ShenYiTan/self-balancing-robot-esp32/docs/images/IMG_20250817_193725.jpg

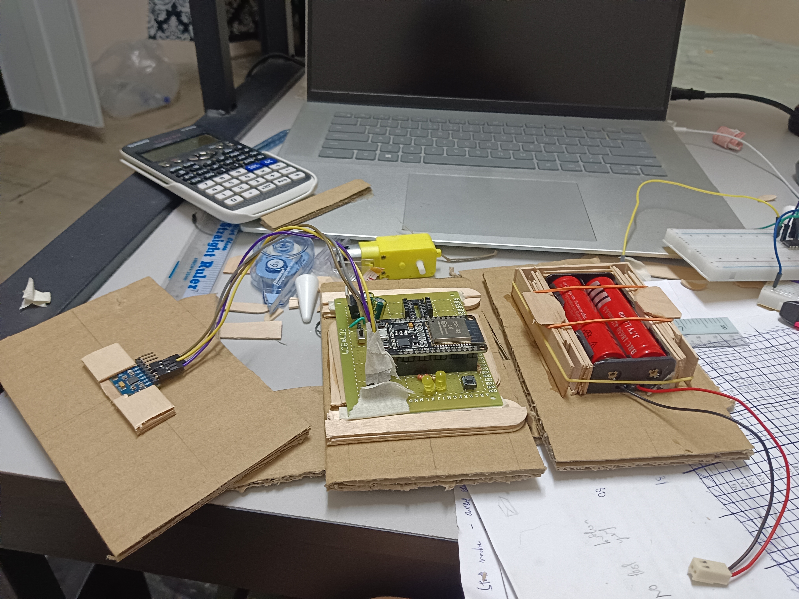
docs/images/IMG_20250817_193725.jpg
