ShenYiTan/self-balancing-robot-esp32/docs/images/IMG_20250912_112348.jpg

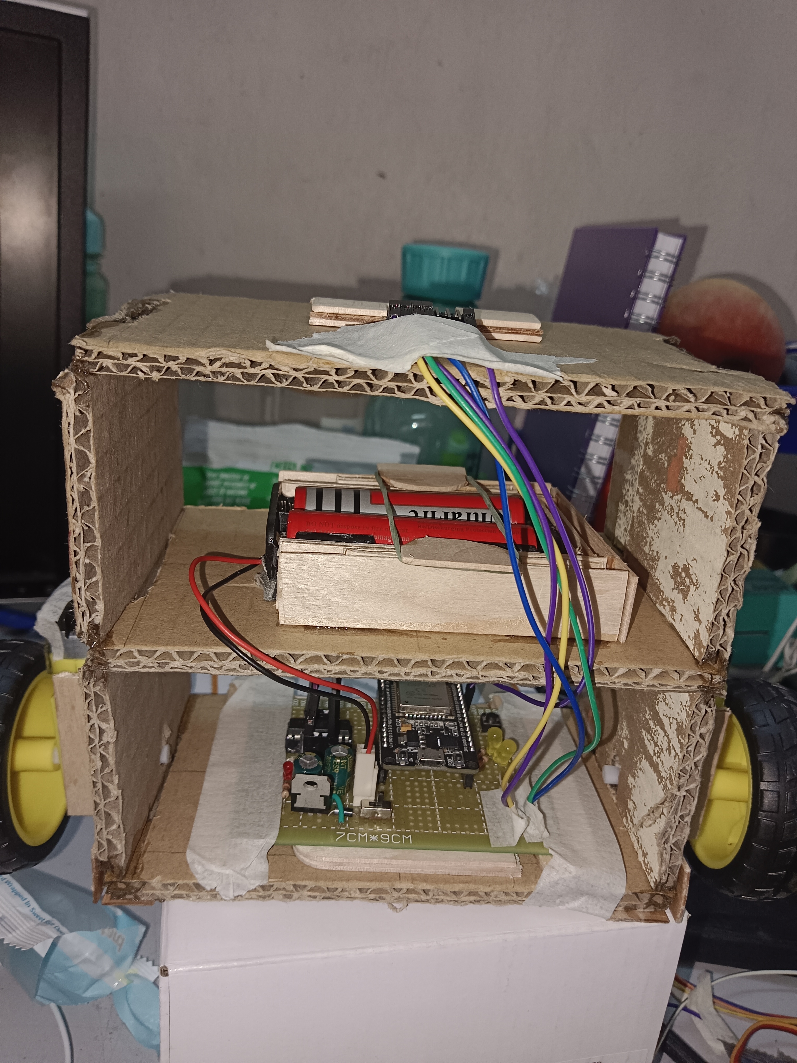
docs/images/IMG_20250912_112348.jpg
