ShenYiTan/self-balancing-robot-esp32/docs/images/IMG_20250912_112354.jpg

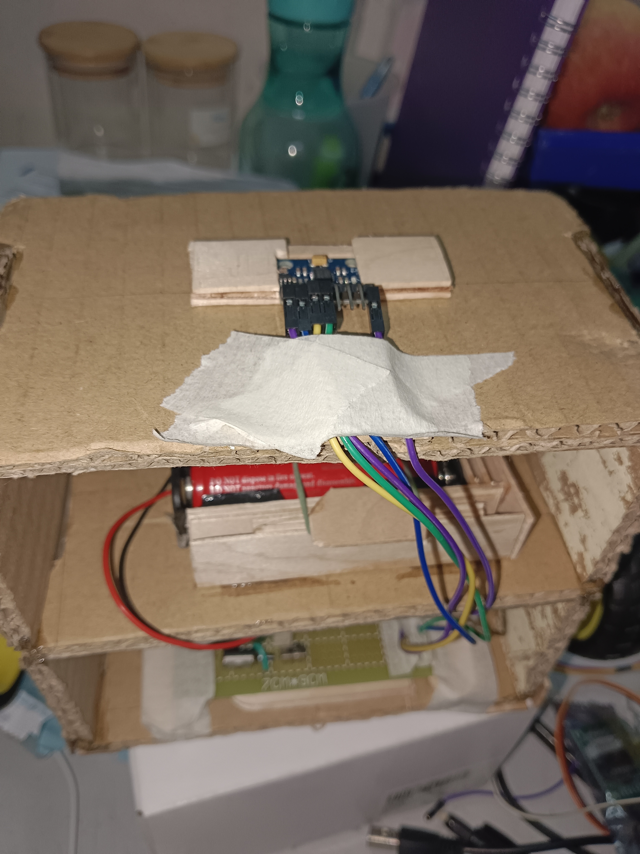
docs/images/IMG_20250912_112354.jpg
