ShenYiTan/self-balancing-robot-esp32/docs/images/IMG_20250916_214443.jpg

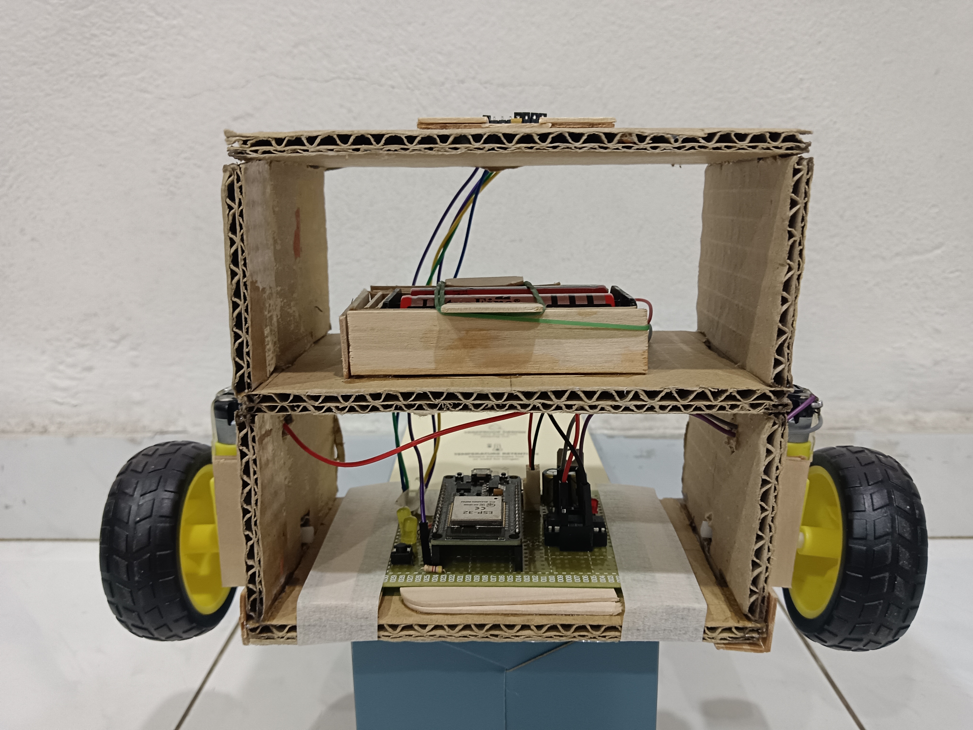
docs/images/IMG_20250916_214443.jpg
