ShenYiTan/self-balancing-robot-esp32/docs/3D_model/tyre.SLDPRT

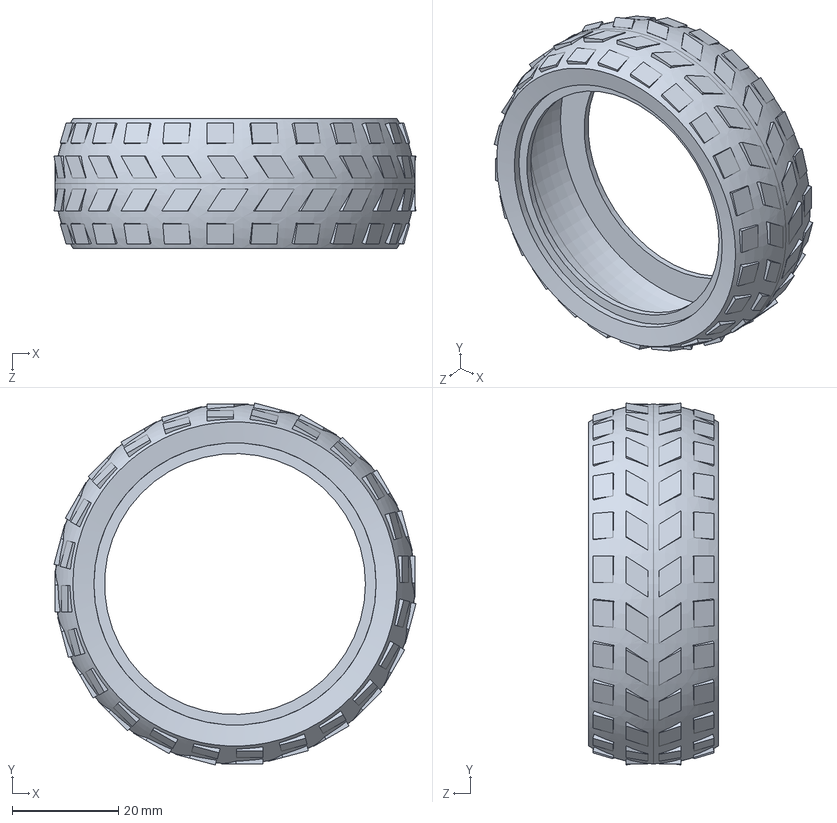
[picture p39: CAD file, 2025-10-01]
docs/3D_model/tyre.SLDPRT
68.0 x 68.0 x 24.4 mm
