ShenYiTan/self-balancing-robot-esp32/docs/3D_model/push button.SLDPRT

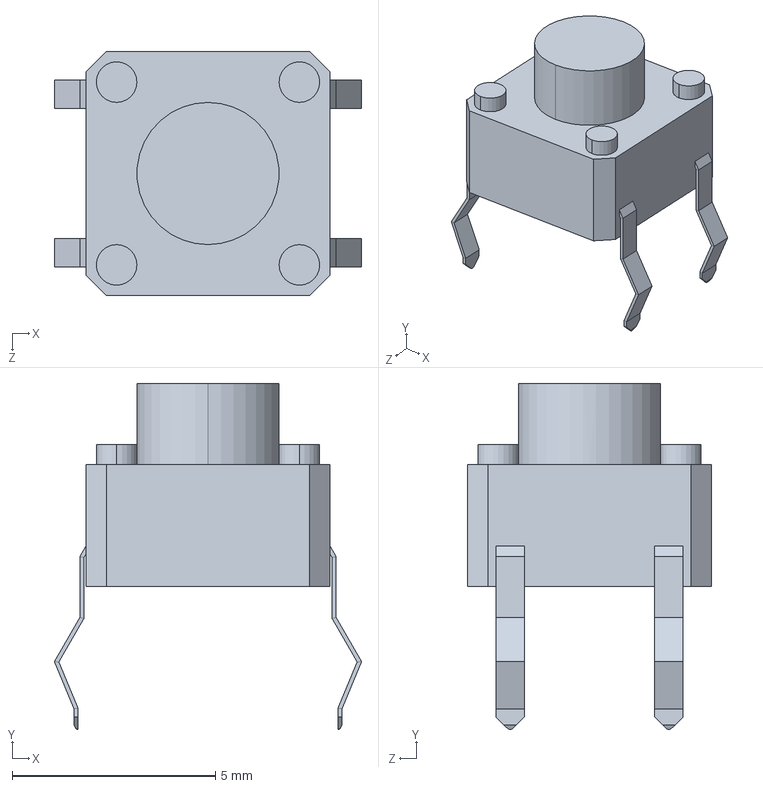
[picture p40: CAD file, 2025-10-01]
docs/3D_model/push button.SLDPRT
7.57 x 8.52 x 6.01 mm
