ShenYiTan/self-balancing-robot-esp32/docs/3D_model/motor shaft.SLDPRT

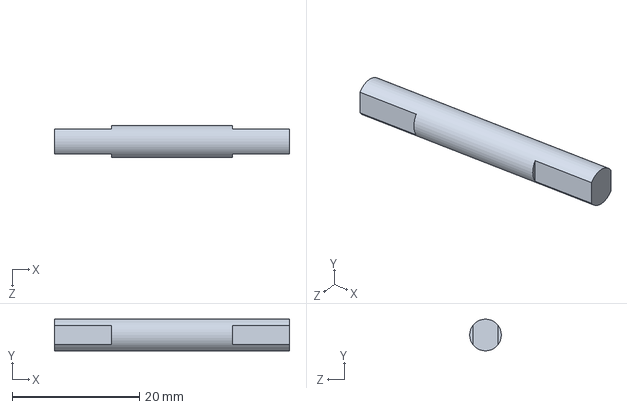
[picture p41: CAD file, 2025-10-01]
docs/3D_model/motor shaft.SLDPRT
37.0 x 5.00 x 5.00 mm
