ShenYiTan/self-balancing-robot-esp32/docs/3D_model/circuit.SLDASM

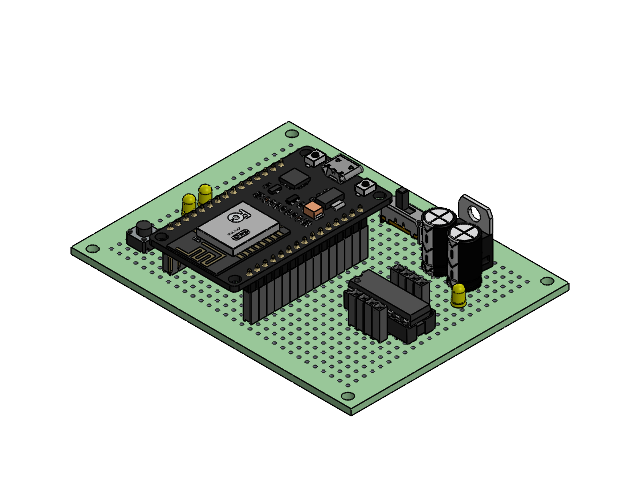
[picture p43: CAD file, 2025-10-01]
docs/3D_model/circuit.SLDASM
perfboard
Female Pin Header.step x 38
DIP16N socket.step
DIP16N IC.step
330uF 25V electr x 2
SlideSwitchSLDPRT
Led 3mm green_ x 3
push button
BUTTONFLASH-13_2.stp x 2
BUTTONFLASH-14_2.stp x 2
PCB.stp
PIN.stp x 30
WIFI_CARD_2.stp
RECTANGULARCHIP_2.stp
MICROCHIP_2.stp
TANCHIP_2.stp
TRANSISTOR_3-LEG_2.stp
RESISTOR1_2.stp x 11
RESISTOR2-32_2.stp x 2
TRANSISTOR_3-LEG2_2.stp
USB_SOCKET_2.stp
