ShenYiTan/self-balancing-robot-esp32/docs/3D_model/GY-521_MPU6050 Accelerometer.SLDASM

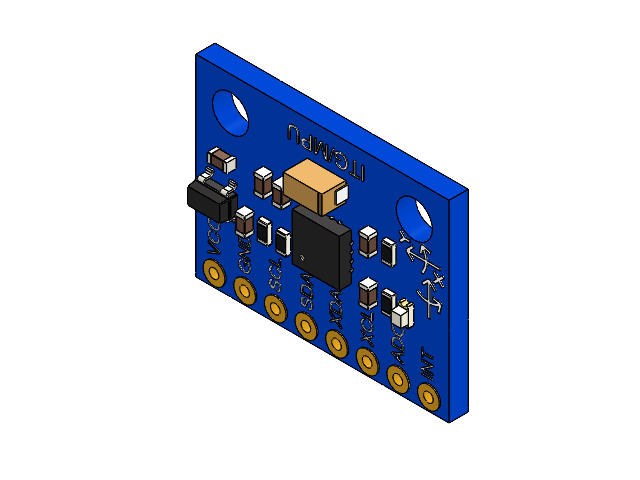
[picture p44: CAD file, 2025-10-01]
docs/3D_model/GY-521_MPU6050 Accelerometer.SLDASM
PCB.step
trou1.step
trou002.step
trou003.step
trou004.step
trou005.step
trou006.step
trou007.step
trou008.step
Text_X.step
Symb_Y.step
Symb_X.step
Text_Y.step
Text_VCC.step
Text_GND.step
Text_SCL.step
Text_SDA.step
Text_XDA.step
Text_XCL.step
Text_ADO.step
Text_INT.step
R_0603_1608Metric.step
R_0603_1608Metric001.step
R_0603_1608Metric002.step
R_0603_1608Metric003.step
C_0603_1608Metric.step
C_0603_1608Metric001.step
C_0603_1608Metric002.step
C_0603_1608Metric003.step
Corps002.step
Corps001 (Mirror #1).step
C_0603_1608Metric004.step
C_0603_1608Metric005.step
LED_0603_1608Metric_Castellated.step
QFN_16_1EP_4x4mm_P065mm_EP21x21mm.step
Text_ITGMPU.step
SOT_23_5.step
Corps001.step
