ShenYiTan/self-balancing-robot-esp32/docs/3D_model/BATTERY HOLDERx2.SLDASM

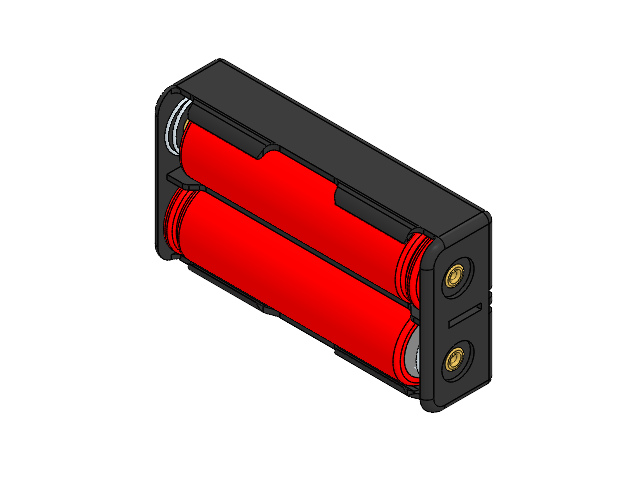
[picture p45: CAD file, 2025-10-01]
docs/3D_model/BATTERY HOLDERx2.SLDASM
Porta baterias 2x18650.stp
Contacto_Helice_v2.0.stp x 2
Contacto_plano_v1.0.stp x 2
Bateria 18650.stp x 2
remache_v1.0.stp x 4
