ShenYiTan/self-balancing-robot-esp32/docs/3D_model/DIP16N socket with IC.SLDASM

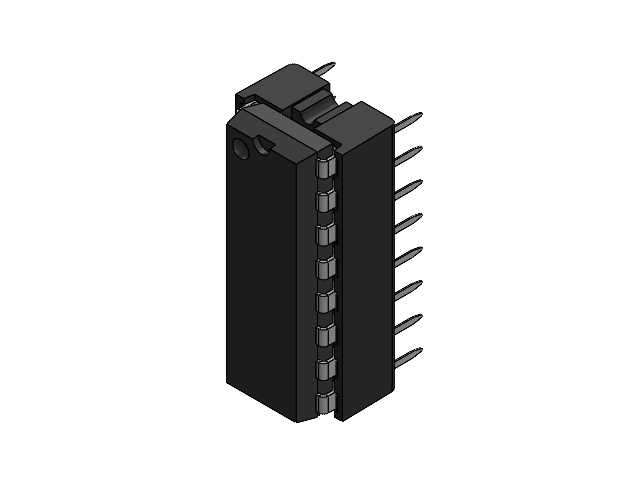
[picture p46: CAD file, 2025-10-01]
docs/3D_model/DIP16N socket with IC.SLDASM
DIP16N socket.step
DIP16N IC.step
